AaronC81/delta-radix/delta-radix-hal-pico/src/hal/keypad.rs

use core::convert::Infallible;

use cortex_m::delay::Delay;
use delta_radix_hal::Key;
use embedded_hal::digital::v2::{InputPin, OutputPin};
use rp_pico::hal::gpio::{bank0::{Gpio15, Gpio16, Gpio17, Gpio18, Gpio19, Gpio20, Gpio21, Gpio22, Gpio26, Gpio27, Gpio28}, Pin, Input, PullUp, Output, PushPull};

type Col0 = Gpio15;
type Col1 = Gpio16;
type Col2 = Gpio17;
type Col3 = Gpio18;
type Col4 = Gpio19;

type Row0 = Gpio20;
type Row1 = Gpio21;
type Row2 = Gpio22;
type Row3 = Gpio26;
type Row4 = Gpio27;
type Row5 = Gpio28;

type ColPin<T> = Pin<T, Input<PullUp>>;
type RowPin<T> = Pin<T, Output<PushPull>>;

pub struct ButtonMatrix<'d> {
    pub delay: &'d mut Delay,

    pub col0: ColPin<Col0>,
    pub col1: ColPin<Col1>,
    pub col2: ColPin<Col2>,
    pub col3: ColPin<Col3>,
    pub col4: ColPin<Col4>,

    pub row0: RowPin<Row0>,
    pub row1: RowPin<Row1>,
    pub row2: RowPin<Row2>,
    pub row3: RowPin<Row3>,
    pub row4: RowPin<Row4>,
    pub row5: RowPin<Row5>,

    pub currently_pressed: Option<(u8, u8)>,
}

impl<'d> ButtonMatrix<'d> {
    const COLS: usize = 5;
    const ROWS: usize = 6;

    const DEBOUNCE_MS: u32 = 1;

    fn rows_and_cols(&mut self) ->
        ([&mut dyn OutputPin<Error = Infallible>; ButtonMatrix::<'d>::ROWS], [&mut dyn InputPin<Error = Infallible>; ButtonMatrix::<'d>::COLS])
    {
        // Borrow splitting FTW!
        (
            [&mut self.row0, &mut self.row1, &mut self.row2, &mut self.row3, &mut self.row4, &mut self.row5],
            [&mut self.col0, &mut self.col1, &mut self.col2, &mut self.col3, &mut self.col4],
        )
    }

    pub fn scan_matrix(&mut self) -> Option<(u8, u8)> {
        let (mut rows, mut cols) = self.rows_and_cols();

        // Set all rows high
        for row in rows.iter_mut() {
            row.set_high().unwrap();
        }

        // Iterate over each row...
        for (r, row) in rows.iter_mut().enumerate() {
            // Set it low
            row.set_low().unwrap();

            // Check each column - if it's low, the button was pressed!
            for (c, col) in cols.iter_mut().enumerate() {
                if col.is_low().unwrap() {
                    return Some((r as u8, c as u8));
                }
            }

            // Put it back to high
            row.set_high().unwrap();
        }

        // Nothing pressed
        None
    }

    pub fn wait_press(&mut self) -> (u8, u8) {
        // If we're currently pressing, wait for a release, or a different press
        if let Some(current_press) = self.currently_pressed {
            loop {
                if self.scan_matrix() != Some(current_press) {
                    // Wait the debounce time, and check that there's still no press
                    self.delay.delay_ms(Self::DEBOUNCE_MS);
                    if self.scan_matrix() != Some(current_press) {
                        break;
                    }
                }
    
                self.delay.delay_ms(Self::DEBOUNCE_MS);
            }
        }

        // Repeatedly scan the matrix until we get a press
        loop {
            if let Some(initial_press) = self.scan_matrix() {
                // Wait the debounce time, and check that the press is the same
                self.delay.delay_ms(Self::DEBOUNCE_MS);
                if let Some(debounce_press) = self.scan_matrix() {
                    if initial_press == debounce_press {
                        // Yep, that's a press! Store it and return
                        self.currently_pressed = Some(initial_press);
                        return initial_press;
                    }
                }
            }

            self.delay.delay_ms(Self::DEBOUNCE_MS);
        }
    }

    pub fn map_key(&self, row: u8, col: u8) -> Option<Key> {
        match (col, row) {
            (4, 5) => Some(Key::Exe),

            (0, 1) => Some(Key::Add),
            (1, 1) => Some(Key::Subtract),
            (2, 1) => Some(Key::Multiply),
            (3, 1) => Some(Key::Divide),

            (4, 1) => Some(Key::Delete),

            (3, 0) => Some(Key::Left),
            (4, 0) => Some(Key::Right),

            (2, 0) => Some(Key::Variable),
            
            (0, 5) => Some(Key::Digit(0)),
            (0, 4) => Some(Key::Digit(1)),
            (1, 4) => Some(Key::Digit(2)),
            (2, 4) => Some(Key::Digit(3)),
            (0, 3) => Some(Key::Digit(4)),
            (1, 3) => Some(Key::Digit(5)),
            (2, 3) => Some(Key::Digit(6)),
            (0, 2) => Some(Key::Digit(7)),
            (1, 2) => Some(Key::Digit(8)),
            (2, 2) => Some(Key::Digit(9)),

            (3, 4) => Some(Key::Digit(0xA)),
            (4, 4) => Some(Key::Digit(0xB)),
            (3, 3) => Some(Key::Digit(0xC)),
            (4, 3) => Some(Key::Digit(0xD)),
            (3, 2) => Some(Key::Digit(0xE)),
            (4, 2) => Some(Key::Digit(0xF)),

            (1, 5) => Some(Key::FormatSelect),
            (2, 5) => Some(Key::HexBase),
            (3, 5) => Some(Key::BinaryBase),

            (0, 0) => Some(Key::Shift),
            (1, 0) => Some(Key::Menu),
            
            _ => None,
        }
    }
}

impl<'d> delta_radix_hal::Keypad for ButtonMatrix<'d> {
    async fn wait_key(&mut self) -> Key {
        loop {
            let (r, c) = self.wait_press();
            if let Some(key) = self.map_key(r, c) {
                return key
            }
        }
    }
}
