AaronC81/delta-radix/delta-radix-hal-pico/build.rs

use std::{path::PathBuf, env, fs::File, io::Write};

fn main() {    
    // Put `memory.x` in our output directory and ensure it's
    // on the linker search path.
    let out = &PathBuf::from(env::var_os("OUT_DIR").unwrap());
    File::create(out.join("memory.x"))
        .unwrap()
        .write_all(include_bytes!("memory.x"))
        .unwrap();
    println!("cargo:rustc-link-search={}", out.display());
}
